ondrejh/smokehouse/sketch/device/transfer.h

#ifndef __TRANSFER_H__
#define __TRANSFER_H__

const uint8_t transf_icon[24] = {
	0x3F, 0xFF, 0xFC, /*  0 */
	0x60, 0x00, 0x06, /*  1 */
	0xC0, 0x00, 0x03, /*  2 */
	0x80, 0x70, 0x01, /*  3 */
	0x83, 0x80, 0x01, /*  4 */
	0x9F, 0xFF, 0xF9, /*  5 */
	0x9F, 0xFF, 0xF9, /*  6 */
	0x83, 0x80, 0x01  /*  7 */
};

#endif
